zeldin/iceGDROM/rv32/source/config.h

#define CPU_FREQ 39513600


/* Define as 1 if the CD pin is shorted to GND when the card is removed */
/* Define as 0 if the CD pin is shorted to GND when the card is inserted */

#define SD_CD_PIN_ACTIVE_HIGH 0


/* Comment out to enable debug printouts on serial port */

#define NDEBUG


/* Uncomment to get extra IDE debug */

/* #define IDEDEBUG */


/* Set to desired baudrate for serial debug output */

#define BAUDRATE 115200


/* Comment out to disable subchannel Q emulation */

#define CDDA_SUBCHANNEL_Q


/* Comment out to disable skipahead index */

#define FATFS_SKIPAHEAD_INDEX
