zeldin/iceGDROM/rv32/source/fatfs.c

#include <stdint.h>
#include <stdbool.h>
#include <string.h>

#include "config.h"

#include "sdcard.h"
#include "fatfs.h"
#include "debug.h"

#define NUM_CACHE_SLOTS 4

static uint8_t cache[NUM_CACHE_SLOTS][512];
static uint32_t cache_block_nr[NUM_CACHE_SLOTS];
static uint8_t cache_lru[NUM_CACHE_SLOTS];
static uint32_t fat_start, data_start, root_dir_start;
static uint16_t root_dir_entries;
static uint8_t cluster_shift, blocks_per_cluster;
static bool fat32;
static uint32_t file_start_cluster;
#ifdef FATFS_SKIPAHEAD_INDEX
#define NUM_SKIPAHEAD_ENTRIES 40
static uint32_t skipahead_index[NUM_SKIPAHEAD_ENTRIES];
#endif

#define FAT_EOC   0x80000000
#define FAT_ERROR 0x40000000

char filename[11] = "DISC0000GI0";
uint8_t fatfs_filenumber = 0;

static void reset_cache()
{
  uint8_t slot;
  for (slot = 0; slot < NUM_CACHE_SLOTS; slot++) {
    cache_block_nr[slot] = ~0;
    cache_lru[slot] = slot;
  }
}

#ifdef FATFS_SKIPAHEAD_INDEX
static void init_skipahead_index()
{
  unsigned i;
  skipahead_index[0] = file_start_cluster;
  for (i=1; i<NUM_SKIPAHEAD_ENTRIES; i++)
    skipahead_index[i] = FAT_EOC|FAT_ERROR;
}
#endif

static uint8_t *read_block(uint32_t nr)
{
  uint8_t slot, xslot = ~0;
  for (slot = 0; slot < NUM_CACHE_SLOTS; slot++) {
    if (nr == cache_block_nr[slot])
      break;
    else if (cache_block_nr[slot] == ~0)
      xslot = slot;
  }
  if (slot >= NUM_CACHE_SLOTS) {
    if (xslot < NUM_CACHE_SLOTS)
      slot = xslot;
    else {
      for (slot = 0; slot < NUM_CACHE_SLOTS-1; slot++) {
	if (cache_lru[slot] == NUM_CACHE_SLOTS-1)
	  break;
      }
    }
  }
  if (nr != cache_block_nr[slot]) {
    cache_block_nr[slot] = nr;
    if (!sd_read_block(nr, cache[slot])) {
      cache_block_nr[slot] = ~0;
      return NULL;
    }
  }
  uint8_t i, old_lru = cache_lru[slot];
  for (i=0; i<NUM_CACHE_SLOTS; i++)
    if (cache_lru[i] < old_lru)
      cache_lru[i]++;
  cache_lru[slot] = 0;
  return cache[slot];
}

static uint8_t *read_cluster_block(uint32_t nr, uint8_t sub)
{
  return read_block(data_start+(nr<<cluster_shift)+sub);
}

static uint32_t get_fat_entry(uint32_t cluster)
{
  uint8_t n;
  if (fat32) {
    n = ((uint8_t)cluster)&0x7f;
    cluster >>= 7;
  } else {
    n = (uint8_t)cluster;
    cluster >>= 8;
  }
  uint8_t *fat_block = read_block(fat_start+cluster);
  if (!fat_block)
    return FAT_ERROR|FAT_EOC;
  if (fat32) {
    cluster = (((uint32_t*)fat_block)[n])&0x0fffffff;
    if (cluster >= 0x0ffffff8)
      cluster |= FAT_EOC;
  } else {
    cluster = ((uint16_t*)fat_block)[n];
    if (((uint16_t)cluster) >= 0xfff8)
      cluster |= FAT_EOC;
  }
  if (cluster < 2)
    cluster |= FAT_ERROR|FAT_EOC;
  return cluster;
}

static bool check_root_block(uint32_t part_start)
{
  uint8_t *data_block = read_block(part_start);
  if (!data_block)
    return false;

  if(data_block[0x1fe] != 0x55 ||
     data_block[0x1ff] != 0xaa)
    return false;

  /* Check file system type */
  if (data_block[82] != 'F' || data_block[83] != 'A' || data_block[84] != 'T')
    return false;

  /* Check required parameters */
  if (data_block[11] != 0 || data_block[12] != 2 || /* 512 bytes per sector */
      (data_block[14] == 0 && data_block[15] == 0) || /* reserved sectors > 0 */
      data_block[16] != 2) /* fat count */
    return false;

  uint8_t i = 0, n = 1;
  do {
    if (data_block[13] == n)
      break;
    i++;
    n<<=1;
  } while(n);
  if (!n)
    return false;
  cluster_shift=i;
  blocks_per_cluster = n;

  uint16_t rds = data_block[17] + (data_block[18]<<8); /* rootDirEntryCount */
  root_dir_entries = rds;
  rds = (rds >> 4) + ((((uint8_t)rds)&0xf)? 1:0);
  uint32_t bpf = *(uint16_t*)(data_block+22); /* sectorsPerFat16 */
  if (!(uint16_t)bpf)
    bpf = *(uint32_t*)(data_block+36); /* sectorsPerFat32 */
  uint32_t ds = *(uint16_t*)(data_block+14) + part_start;
  fat_start = ds;
  ds += bpf<<1;
  root_dir_start = ds;
  ds += rds;
  data_start = ds - (((uint16_t)2)<<i);
  uint32_t cc = data_block[19] + (data_block[20] << 8); /* totalSectors16 */
  if (!(uint16_t)cc)
    cc = *(uint32_t*)(data_block+32); /* totalSectors32 */
  cc -= (ds - part_start);
  cc >>= i;
  if (cc < 65525) {
    if (((uint16_t)cc) < 4085) {
      /* FAT12 not supported */
      return false;
    }
    fat32 = false;
  } else {
    fat32 = true;
    root_dir_start = *(uint32_t*)(data_block+44);
  }

  DEBUG_PUTS("Mounted fs with ");
  DEBUG_PUTX((uint8_t)(cc>>24));
  DEBUG_PUTX((uint8_t)(cc>>16));
  DEBUG_PUTX((uint8_t)(cc>>8));
  DEBUG_PUTX((uint8_t)cc);
  DEBUG_PUTS(" clusters\n");

  return true;
}

bool fatfs_mount()
{
  reset_cache();
  if (check_root_block(0))
    return true;
  /* Not a valid FAT root block at 0, check for partition table */
  uint8_t *data_block = read_block(0);
  if(!data_block ||
     data_block[0x1fe] != 0x55 ||
     data_block[0x1ff] != 0xaa)
    return false;
  if ((data_block[0x1be] & 0x7f) != 0)
    return false;
  uint32_t part_start = *(uint16_t*)(data_block+0x1c6);
  part_start += (*(uint16_t*)(data_block+0x1c8)) << 16;
  if (!part_start)
    return false;
  return check_root_block(part_start);
}

bool fatfs_read_rootdir()
{
  uint32_t blk = root_dir_start;
  uint16_t rde = root_dir_entries;
  uint8_t entry = 0, cnr = 0;
  const uint8_t *p;
  for (;;) {
    if (!fat32 && !rde)
      break;
    if (!entry) {
      if (fat32) {
	p = read_cluster_block(blk, cnr++);
      } else {
	p = read_block(blk++);
      }
      if (!p)
	return false;
    }
    if (!*p)
      break;
    if (*p != 0xe5 && (p[11]&0x3f) != 0x0f) {
      DEBUG_PUTS("Entry ");
      int i;
      for(i=0; i<11; i++)
	DEBUG_PUTC(p[i]);
      DEBUG_PUTC('\n');
      if (!memcmp(p, filename, 11)) {
	DEBUG_PUTS("Found target at ");
	if (fat32) {
	  DEBUG_PUTX(p[21]);
	  DEBUG_PUTX(p[20]);
	}
	DEBUG_PUTX(p[27]);
	DEBUG_PUTX(p[26]);
	DEBUG_PUTC('\n');
	file_start_cluster = *(uint16_t *)(p+26);
	if (fat32) {
	  file_start_cluster |= (*(uint16_t *)(p+20)) << 16;
	}
#ifdef FATFS_SKIPAHEAD_INDEX
	init_skipahead_index();
#endif
	return true;
      }
    }
    p += 32;
    --rde;
    if (++entry == 16) {
      entry = 0;
      if (fat32) {
	if (cnr == blocks_per_cluster) {
	  cnr = 0;
	  blk = get_fat_entry(blk);
	  if (blk & FAT_EOC)
	    break;
	}
      }
    }
  }
  return false;
}

bool fatfs_seek(struct fatfs_handle *handle, uint32_t sector_nr)
{
  uint32_t hpos = handle->pos & ~(blocks_per_cluster-1);
#ifdef FATFS_SKIPAHEAD_INDEX
  uint32_t idx = sector_nr >> 16;
  if (idx > NUM_SKIPAHEAD_ENTRIES)
    idx = NUM_SKIPAHEAD_ENTRIES - 1;
  while (idx > 0 && (skipahead_index[idx] & FAT_ERROR))
    --idx;
  if (hpos > sector_nr || hpos < (idx << 16)) {
    hpos = idx << 16;
    handle->cluster_nr = skipahead_index[idx];
  }
#else
  if (hpos > sector_nr) {
    handle->cluster_nr = file_start_cluster;
    hpos = 0;
  }
#endif
  while((sector_nr ^ hpos) >= blocks_per_cluster) {
    if (handle->cluster_nr & FAT_EOC)
      break;
    handle->cluster_nr = get_fat_entry(handle->cluster_nr);
    hpos += blocks_per_cluster;
#ifdef FATFS_SKIPAHEAD_INDEX
    if (!(hpos & 0xffffu)) {
      uint32_t idx = hpos >> 16;
      if (idx < NUM_SKIPAHEAD_ENTRIES)
	skipahead_index[idx] = handle->cluster_nr;
    }
#endif
  }
  handle->pos = sector_nr;
  return true;
}

bool fatfs_read_next_sector(struct fatfs_handle *handle, uint8_t *buf)
{
  if (handle->cluster_nr & FAT_EOC)
    return false;
  uint8_t blk = (handle->pos&0xff)&(blocks_per_cluster-1);
  if (buf) {
    if (!sd_read_block(data_start+(handle->cluster_nr<<cluster_shift)+blk, buf))
      return false;
  }
  if (++blk == blocks_per_cluster)
    handle->cluster_nr = get_fat_entry(handle->cluster_nr);
  handle->pos++;
#ifdef FATFS_SKIPAHEAD_INDEX
  if (!(handle->pos & 0xffffu)) {
    uint32_t idx = handle->pos >> 16;
    if (idx < NUM_SKIPAHEAD_ENTRIES)
      skipahead_index[idx] = handle->cluster_nr;
  }
#endif
  return true;
}


bool fatfs_read_header(void *buf, uint16_t size, uint8_t blk)
{
  uint32_t clu = file_start_cluster;
  while (blk >= blocks_per_cluster) {
    clu = get_fat_entry(clu);
    if (clu & FAT_EOC)
      return false;
    blk -= blocks_per_cluster;
  }
  uint8_t *data_block = read_cluster_block(clu, blk);
  if (!data_block)
    return false;
  memcpy(buf, data_block, size);
  return true;
}

void fatfs_reset_filename()
{
  memset(filename+4, '0', 4);
  fatfs_filenumber = 0;
}

void fatfs_next_filename()
{
  char *p = filename+8;
  while (*--p <= '9') {
    if (*p == '9') {
      *p = '0';
    } else {
      (*p)++;
      break;
    }
  }
  fatfs_filenumber++;
}
